brianwhitet-ops/stat-puck/design/instinct-firmware-goldens-pr1/02-stroke-edit.png

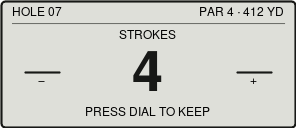
design/instinct-firmware-goldens-pr1/02-stroke-edit.png
