brianwhitet-ops/stat-puck/design/instinct-firmware-goldens-pr1/06-derived-stats.png

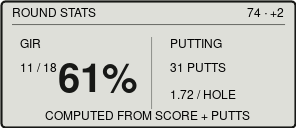
design/instinct-firmware-goldens-pr1/06-derived-stats.png
