brianwhitet-ops/stat-puck/design/instinct-firmware-goldens-pr1/slab-screen-states-contact-sheet.png

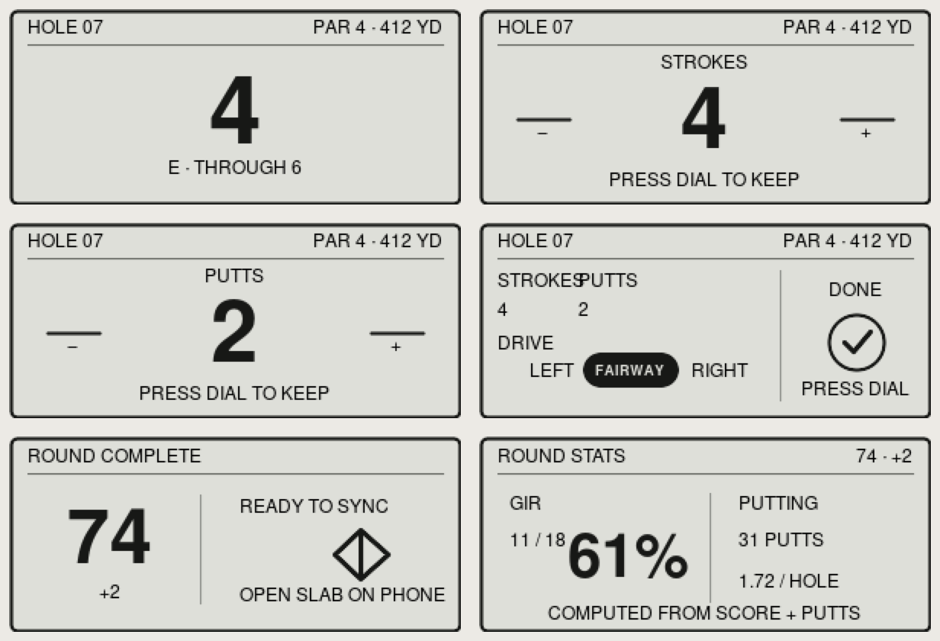
design/instinct-firmware-goldens-pr1/slab-screen-states-contact-sheet.png
