brianwhitet-ops/stat-puck/docs/bench/slab-p1-breadboard-wiring-map.jpg

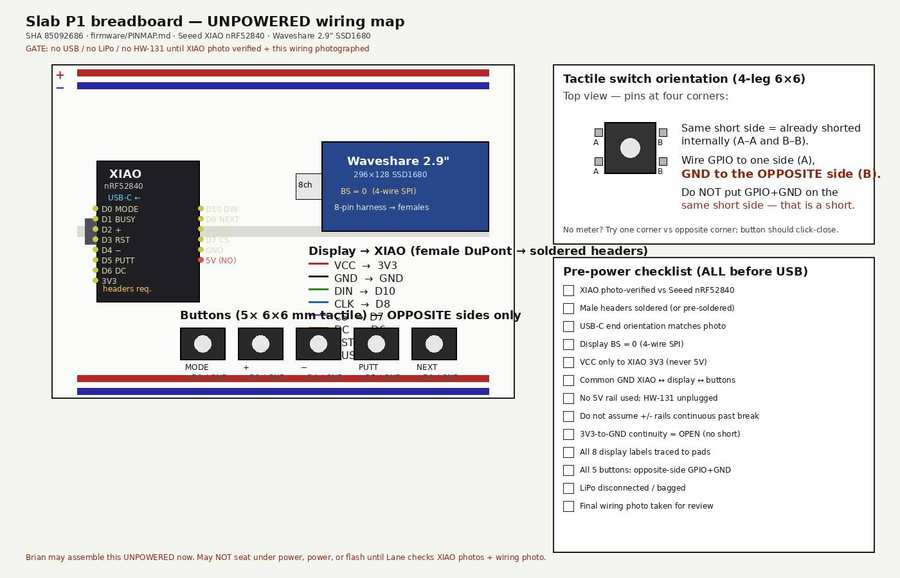
docs/bench/slab-p1-breadboard-wiring-map.jpg
