brianwhitet-ops/stat-puck/docs/bench/slab-p1-row-specific-wiring-map.jpg

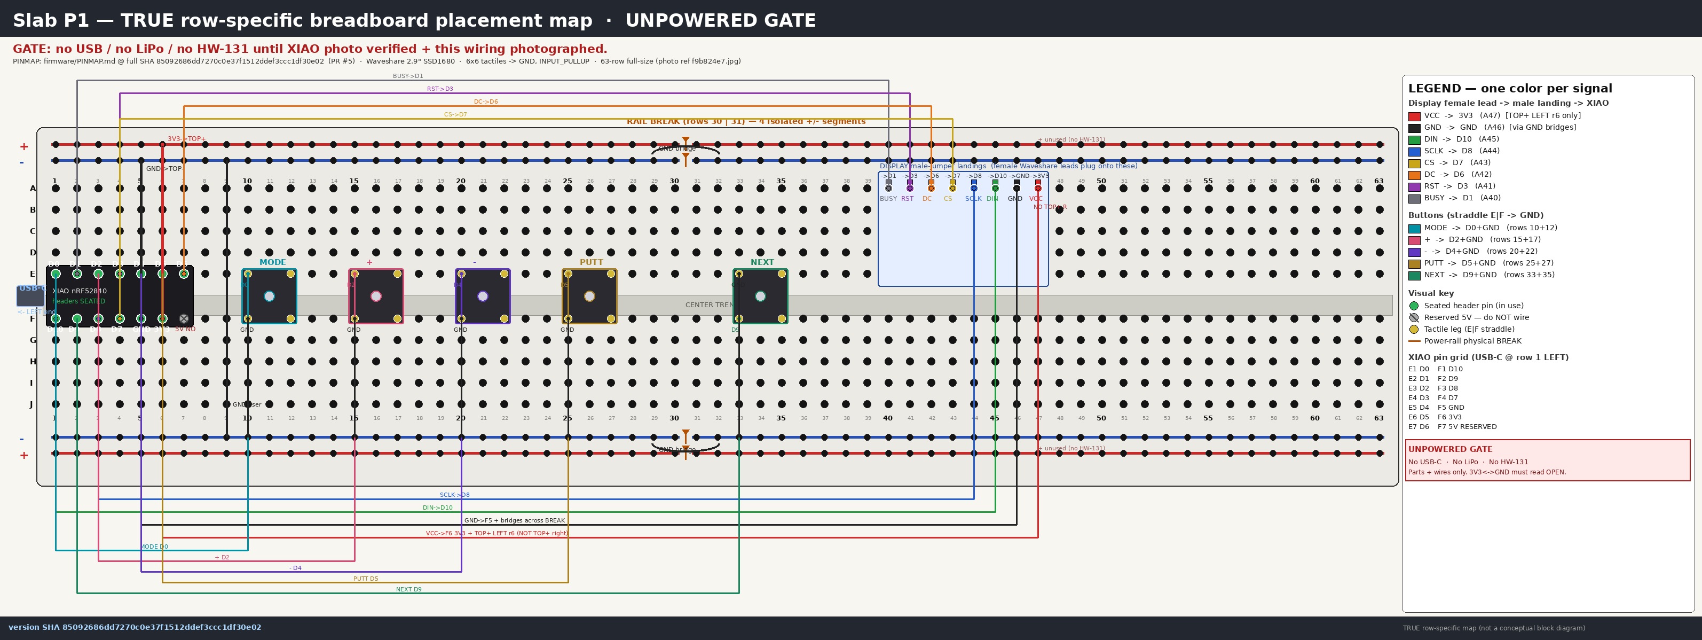
docs/bench/slab-p1-row-specific-wiring-map.jpg
