brianwhitet-ops/stat-puck/firmware/src/slab_font.c

/* SPDX-License-Identifier: MIT */
/*
 * Slab Mono cells — 1-bit raster of DejaVu Sans Mono (Bitstream Vera / Arev).
 * Not Apple SF. DejaVu license: firmware/fonts/dejavu-license.txt
 */
#include "slab_font.h"

static const uint8_t kFontS[1152] = {
    0x00, 0x00, 0x00, 0x00, 0x00, 0x00, 0x00, 0x00, 0x00, 0x00, 0x00, 0x00, /*   */
    0x00, 0x00, 0x10, 0x10, 0x10, 0x10, 0x10, 0x10, 0x00, 0x10, 0x00, 0x00, /* ! */
    0x00, 0x00, 0x28, 0x28, 0x28, 0x00, 0x00, 0x00, 0x00, 0x00, 0x00, 0x00, /* " */
    0x00, 0x00, 0x14, 0x2C, 0xFE, 0x28, 0x28, 0xFC, 0x50, 0x50, 0x00, 0x00, /* # */
    0x00, 0x00, 0x10, 0x3C, 0x50, 0x50, 0x38, 0x1C, 0x14, 0x78, 0x10, 0x10, /* $ */
    0x00, 0x00, 0x60, 0x90, 0x64, 0x18, 0x20, 0x5C, 0x16, 0x1C, 0x00, 0x00, /* % */
    0x00, 0x00, 0x38, 0x60, 0x60, 0x60, 0xD6, 0x8C, 0xCC, 0x7C, 0x00, 0x00, /* & */
    0x00, 0x00, 0x10, 0x10, 0x10, 0x00, 0x00, 0x00, 0x00, 0x00, 0x00, 0x00, /* ' */
    0x00, 0x18, 0x10, 0x10, 0x30, 0x20, 0x20, 0x30, 0x10, 0x10, 0x18, 0x00, /* ( */
    0x00, 0x20, 0x30, 0x10, 0x10, 0x10, 0x10, 0x10, 0x10, 0x30, 0x20, 0x00, /* ) */
    0x00, 0x00, 0x10, 0x54, 0x38, 0x38, 0x54, 0x10, 0x00, 0x00, 0x00, 0x00, /* * */
    0x00, 0x00, 0x00, 0x00, 0x10, 0x10, 0xFC, 0x10, 0x10, 0x00, 0x00, 0x00, /* + */
    0x00, 0x00, 0x00, 0x00, 0x00, 0x00, 0x00, 0x00, 0x10, 0x30, 0x20, 0x00, /* , */
    0x00, 0x00, 0x00, 0x00, 0x00, 0x00, 0x38, 0x00, 0x00, 0x00, 0x00, 0x00, /* - */
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
    0x00, 0x00, 0x00, 0x00, 0x3F, 0x80, 0x30, 0x00, 0x30, 0x00, 0x30, 0x00, 0x30, 0x00, 0x3F, 0x00, 0x30, 0x00, 0x30, 0x00, 0x30, 0x00, 0x30, 0x00, 0x30, 0x00, 0x30, 0x00, 0x00, 0x00, 0x00, 0x00, /* F */
    0x00, 0x00, 0x00, 0x00, 0x1F, 0x00, 0x31, 0x00, 0x60, 0x00, 0x60, 0x00, 0x60, 0x00, 0x60, 0x00, 0x67, 0x80, 0x61, 0x80, 0x61, 0x80, 0x61, 0x80, 0x31, 0x80, 0x1F, 0x00, 0x00, 0x00, 0x00, 0x00, /* G */
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
};

static const uint8_t kMiddotS[12] = { 0x00, 0x00, 0x00, 0x00, 0x00, 0x30, 0x30, 0x00, 0x00, 0x00, 0x00, 0x00 };

const uint8_t *slab_glyph_s(char c)
{
    unsigned char u = (unsigned char)c;
    if (u == 0xB7) {
        return kMiddotS;
    }
    if (u < 32 || u > 127) {
        return &kFontS[0];
    }
    return &kFontS[(u - 32) * 12];
}

const uint8_t *slab_glyph_m(char c)
{
    unsigned char u = (unsigned char)c;
    if (u < 32 || u > 127) {
        return &kFontM[0];
    }
    return &kFontM[(u - 32) * 32];
}
